antmicro/infrared-irradiance-probe/assets/previews/layer1.png

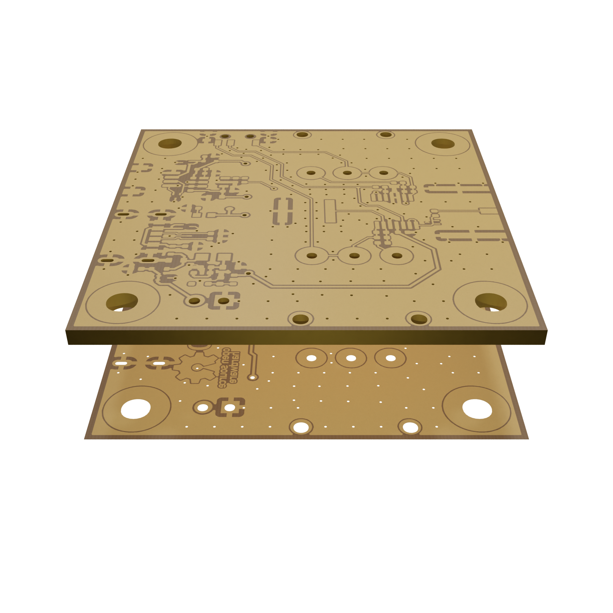
assets/previews/layer1.png
