antmicro/infrared-irradiance-probe/assets/previews/layer2.png

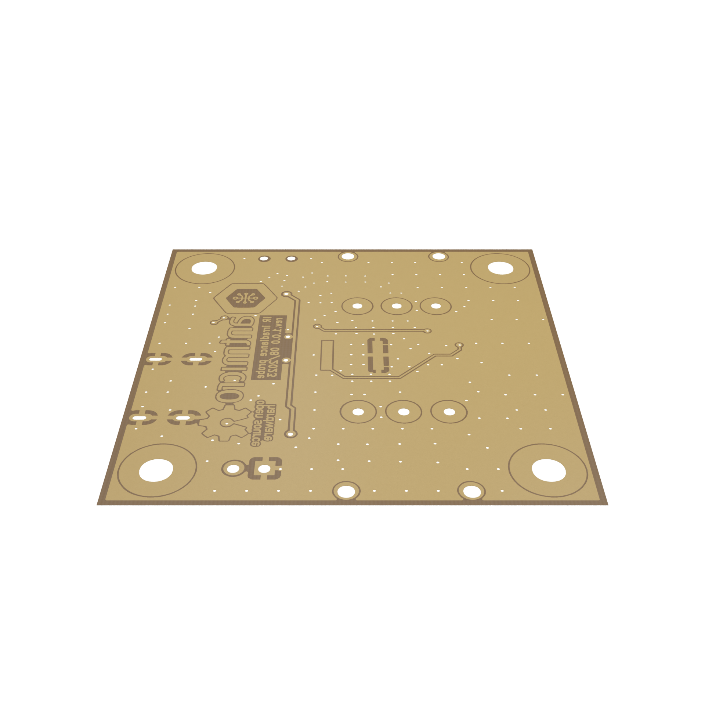
assets/previews/layer2.png
