antmicro/infrared-irradiance-probe/assets/previews/leftB.png

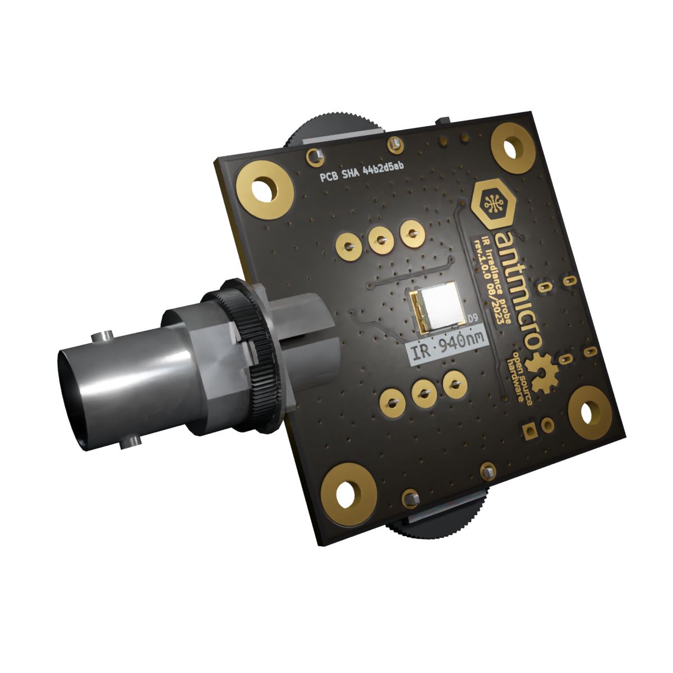
assets/previews/leftB.png
