antmicro/infrared-irradiance-probe/assets/previews/orthoB.png

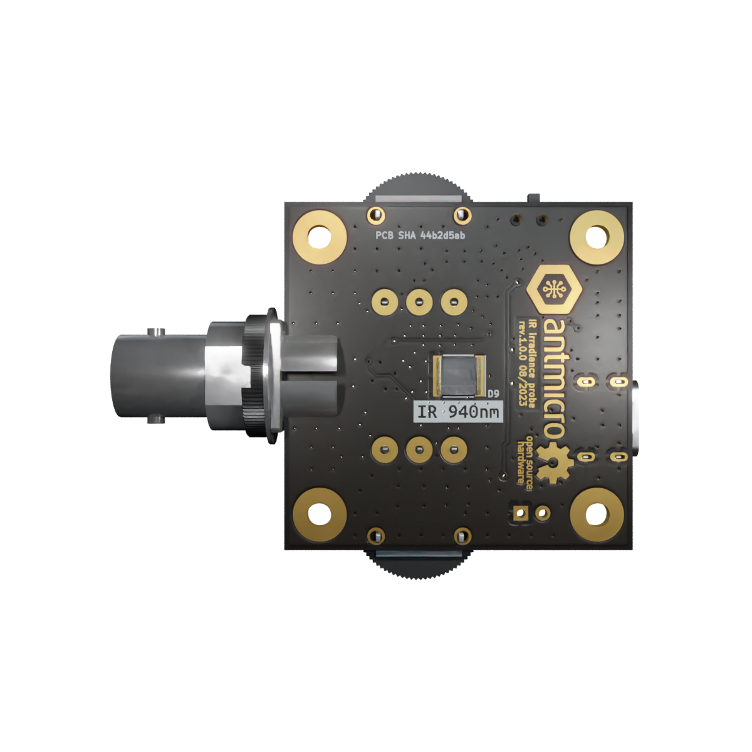
assets/previews/orthoB.png
