antmicro/infrared-irradiance-probe/assets/previews/orthoT.png

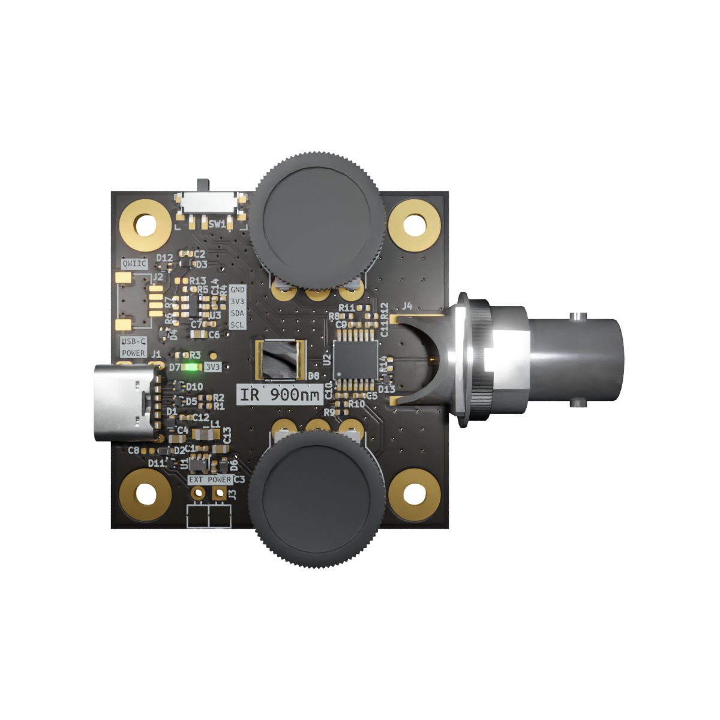
assets/previews/orthoT.png
