antmicro/infrared-irradiance-probe/assets/previews/photoB.png

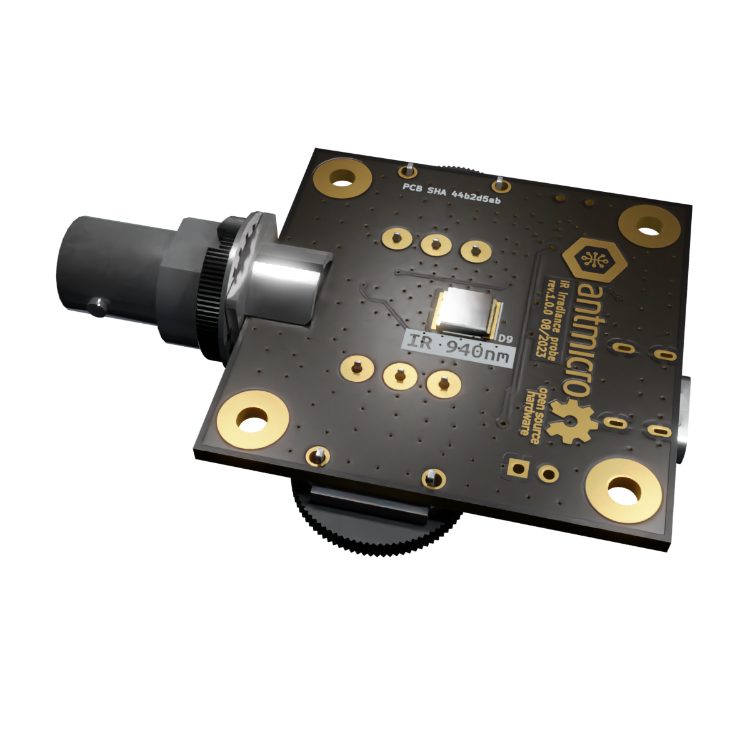
assets/previews/photoB.png
