antmicro/infrared-irradiance-probe/assets/previews/photoT.png

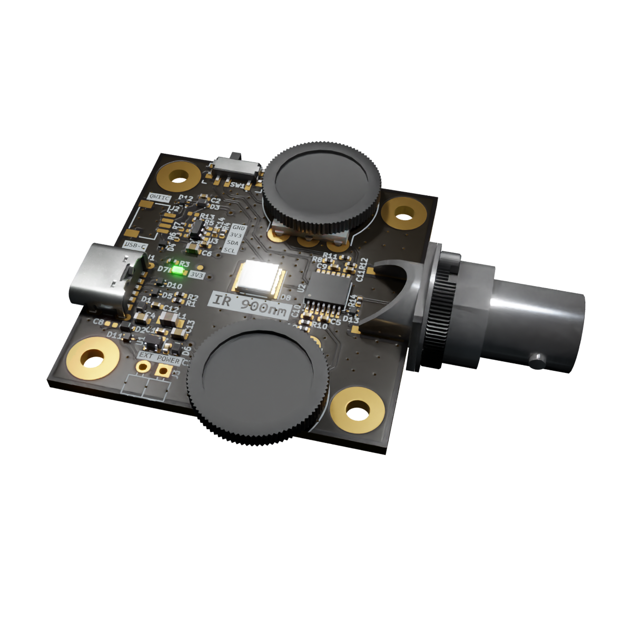
assets/previews/photoT.png
