antmicro/infrared-irradiance-probe/assets/previews/rightB.png

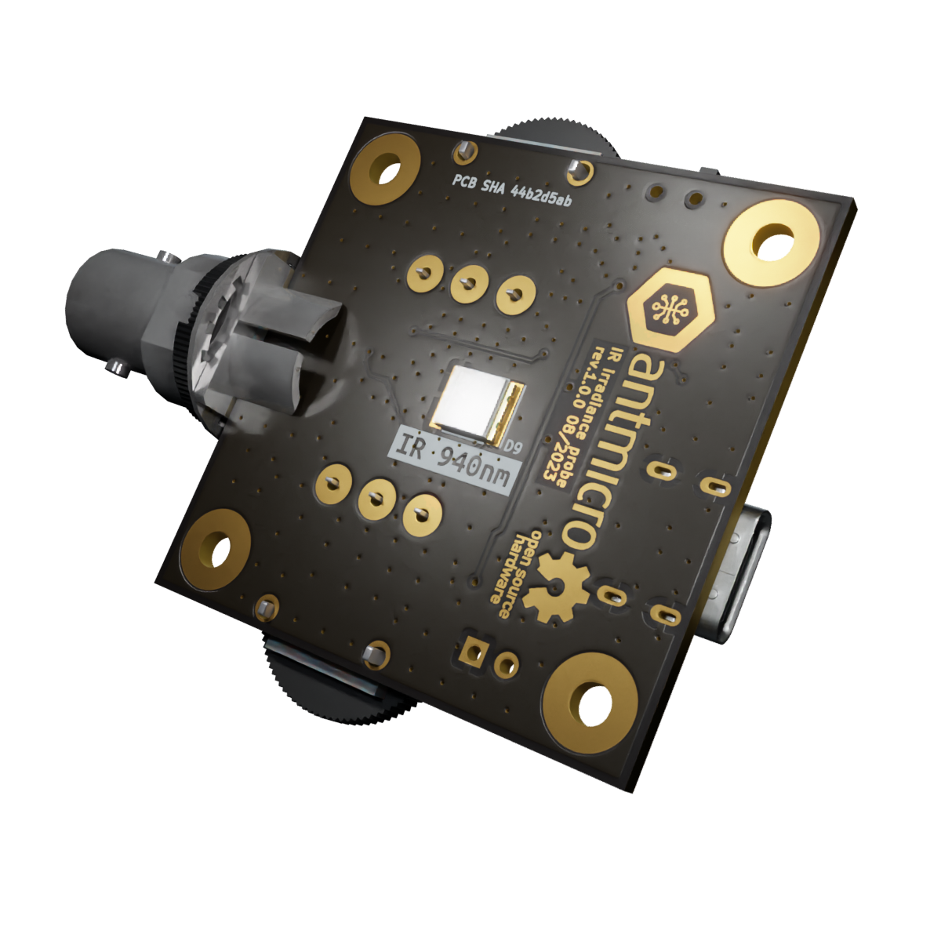
assets/previews/rightB.png
